Tuang8ee/SmartRecycleBin/Project/CAD/ThungRac/ThungKL_Nhua/AnhCocauNghienVoNhua_1.jpg

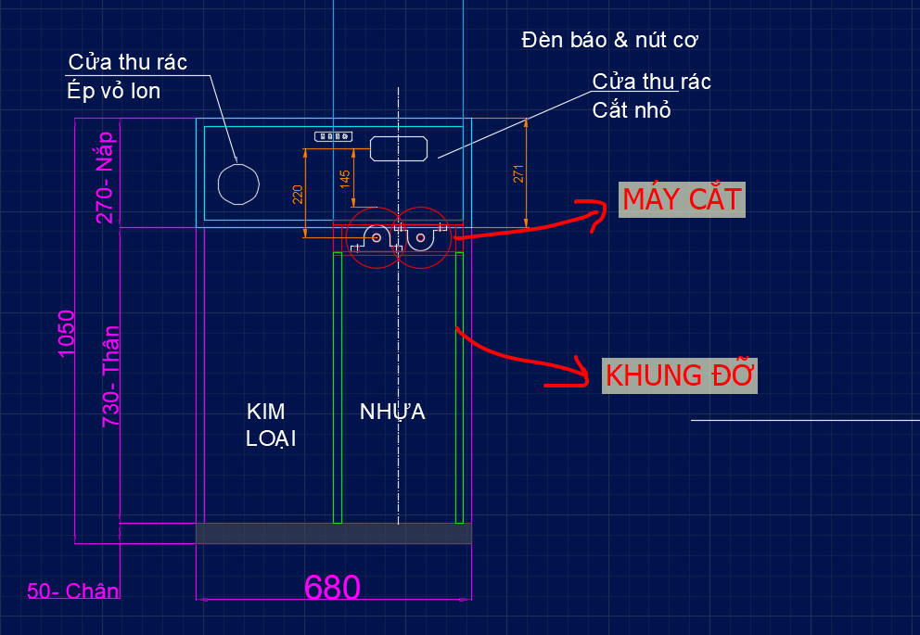
Project/CAD/ThungRac/ThungKL_Nhua/AnhCocauNghienVoNhua_1.jpg
