Tuang8ee/SmartRecycleBin/Project/CAD/ThungRac/ThungKL_Nhua/AnhCocauNghienVoNhua_2.jpg

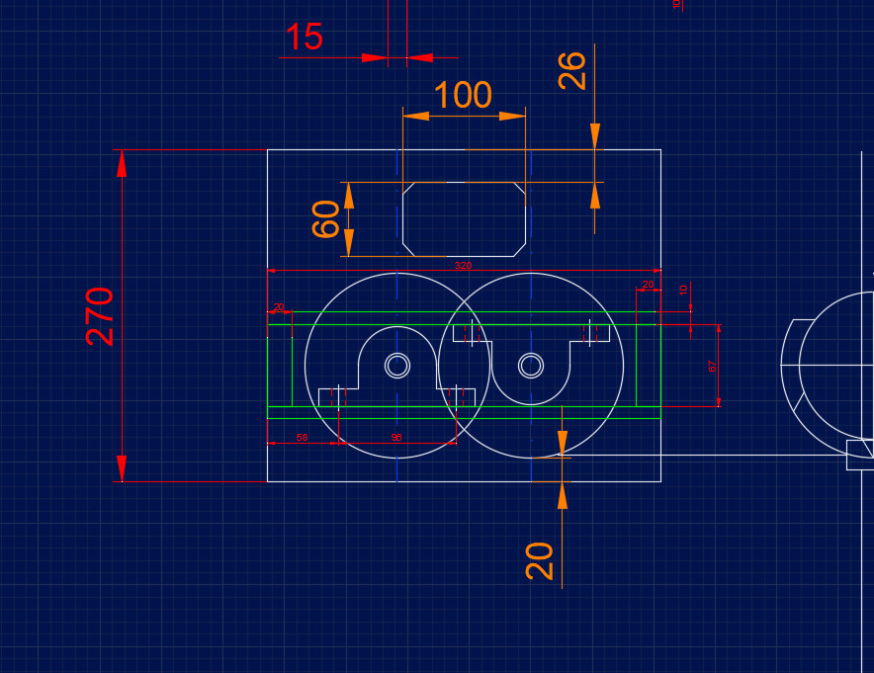
Project/CAD/ThungRac/ThungKL_Nhua/AnhCocauNghienVoNhua_2.jpg
