Tuang8ee/SmartRecycleBin/Report/IMG/z3350971797533_e74e3346405ee866cc10981217ea934d.jpg

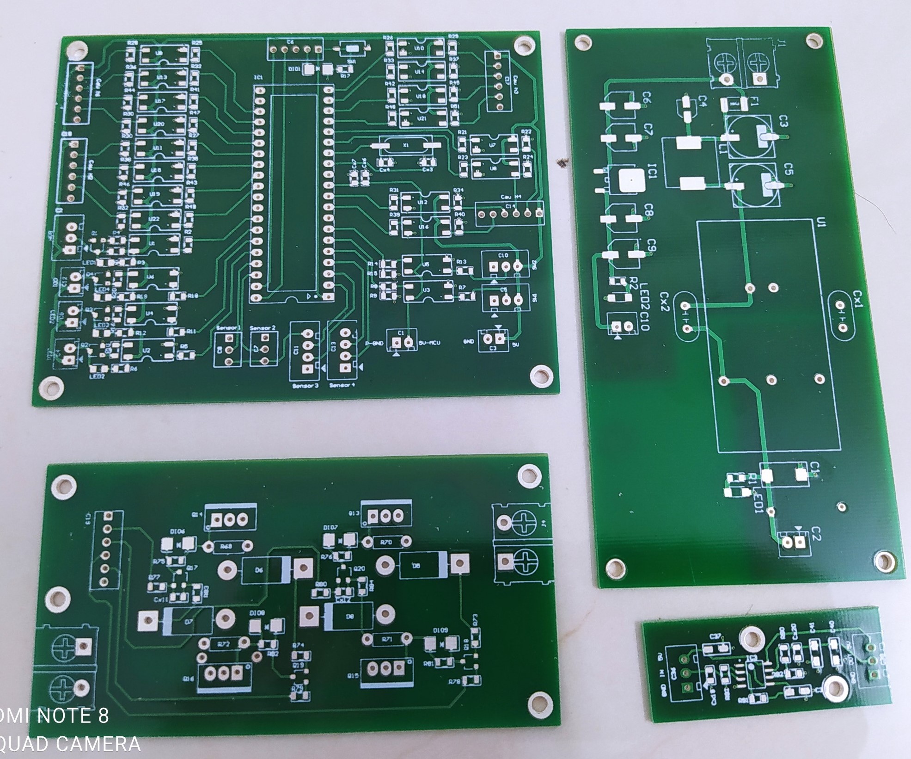
Report/IMG/z3350971797533_e74e3346405ee866cc10981217ea934d.jpg
