Tuang8ee/SmartRecycleBin/Report/IMG/z3350971799951_f81bc6857dea39808778af6e33a4ab04.jpg

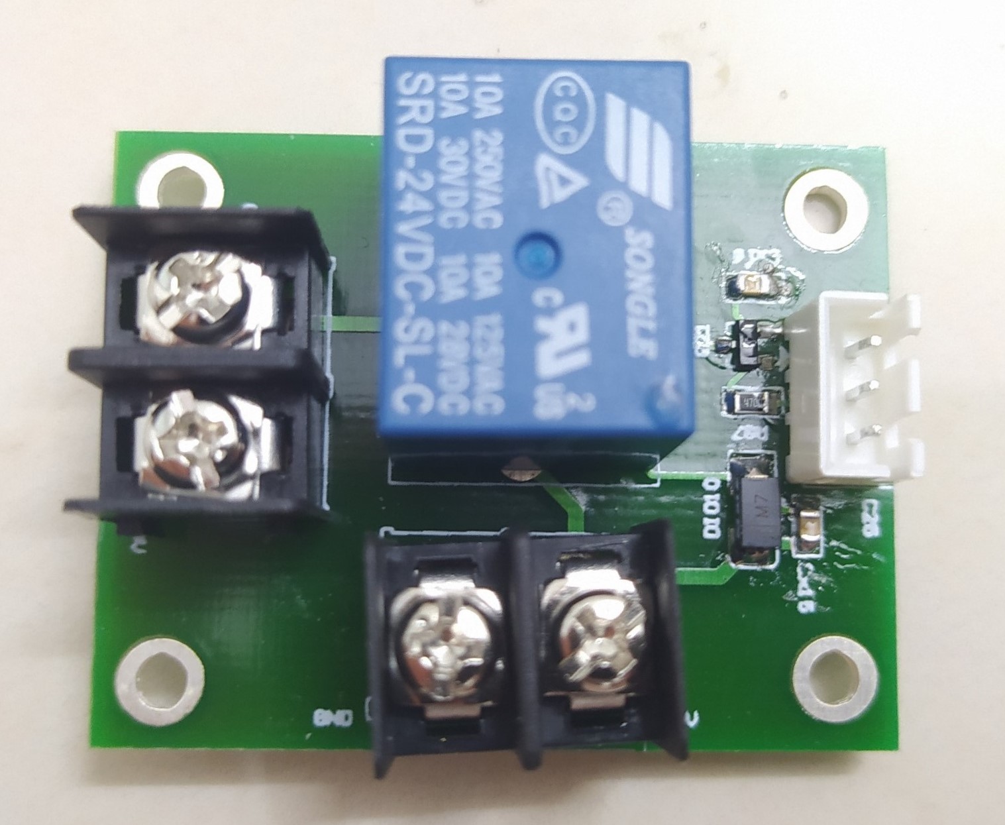
Report/IMG/z3350971799951_f81bc6857dea39808778af6e33a4ab04.jpg
