Tuang8ee/SmartRecycleBin/Report/IMG/z3350971800552_80eb1a36aaf828dc6509fbc643d5b15d.jpg

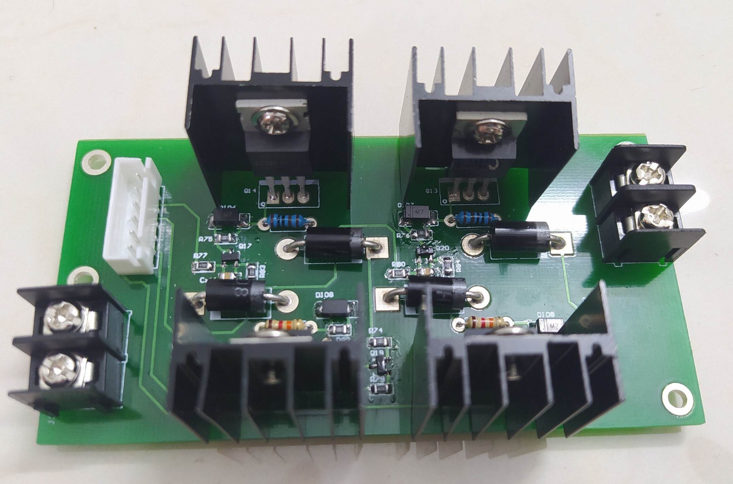
Report/IMG/z3350971800552_80eb1a36aaf828dc6509fbc643d5b15d.jpg
