Tuang8ee/SmartRecycleBin/Report/IMG/z3350971802485_70b66bd4bab3340eb6d8cfec86ee5f43.jpg

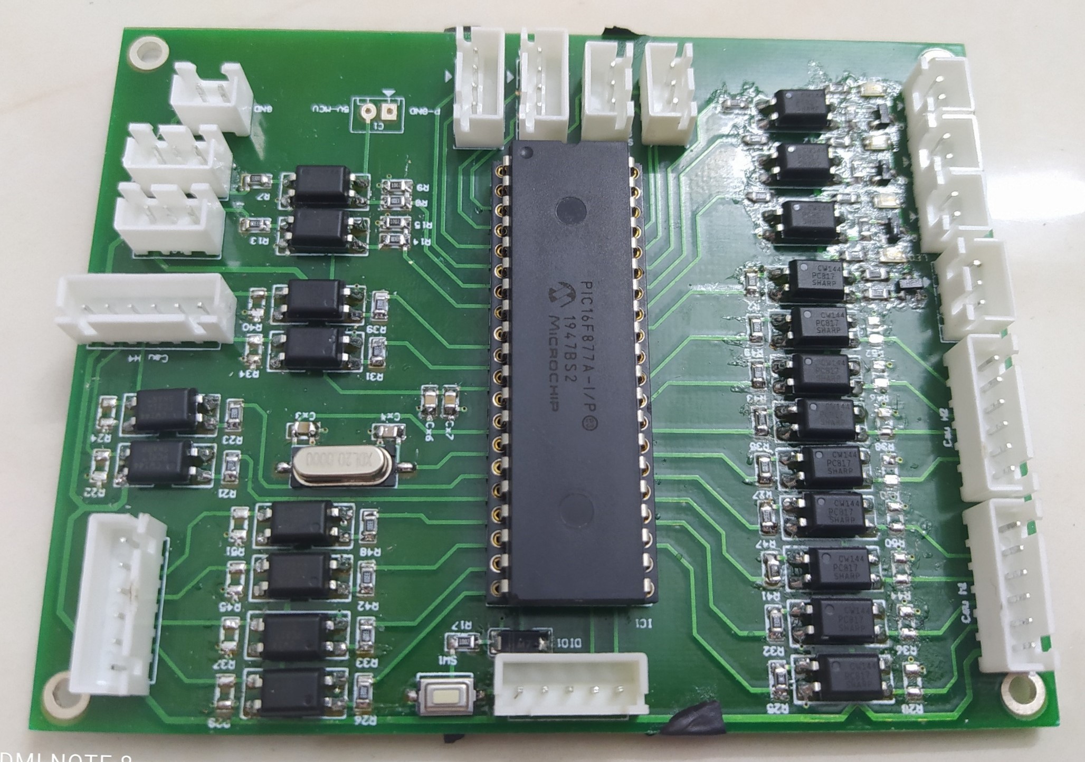
Report/IMG/z3350971802485_70b66bd4bab3340eb6d8cfec86ee5f43.jpg
