Tuang8ee/SmartRecycleBin/Report/IMG/z3350971803121_91358038da6f96965107a016737c2b8c.jpg

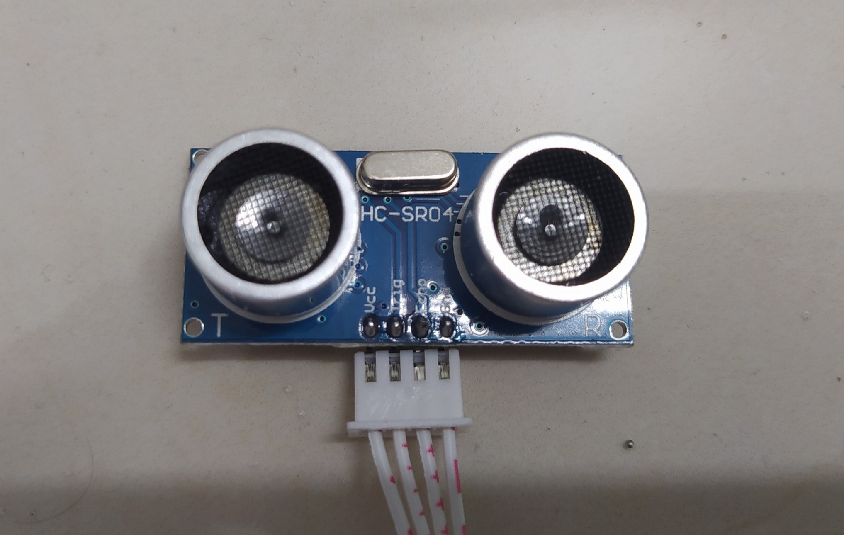
Report/IMG/z3350971803121_91358038da6f96965107a016737c2b8c.jpg
