Tuang8ee/SmartRecycleBin/Report/IMG/z3350971803122_7163d0be3d43af4151d32110a8dd91e1.jpg

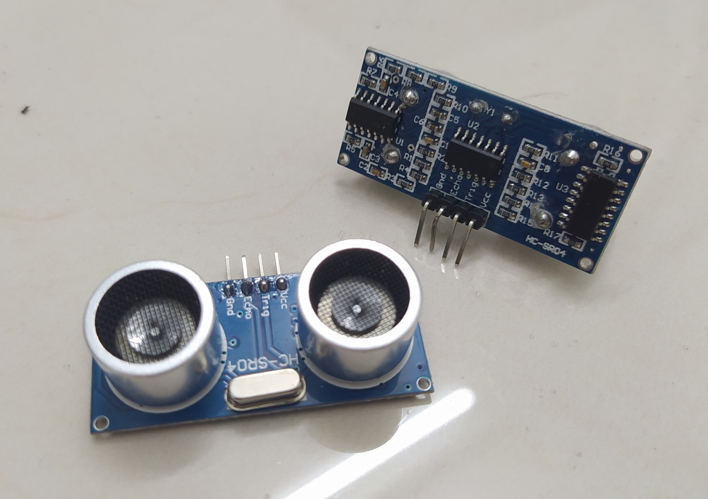
Report/IMG/z3350971803122_7163d0be3d43af4151d32110a8dd91e1.jpg
