Tuang8ee/SmartRecycleBin/Report/IMG/z3350971805743_a142735bbfeaa44c15cc64908d8d2765.jpg

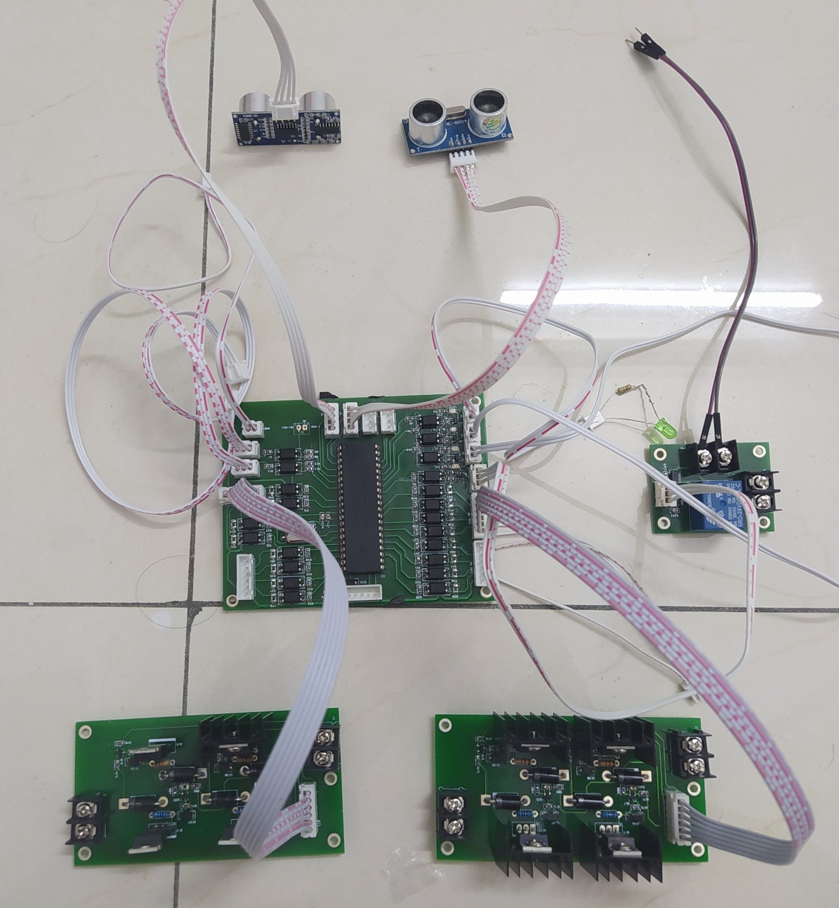
Report/IMG/z3350971805743_a142735bbfeaa44c15cc64908d8d2765.jpg
