Tuang8ee/SmartRecycleBin/Report/IMG/z3350971805745_b5374c409a4009194ae9360d5b574b62.jpg

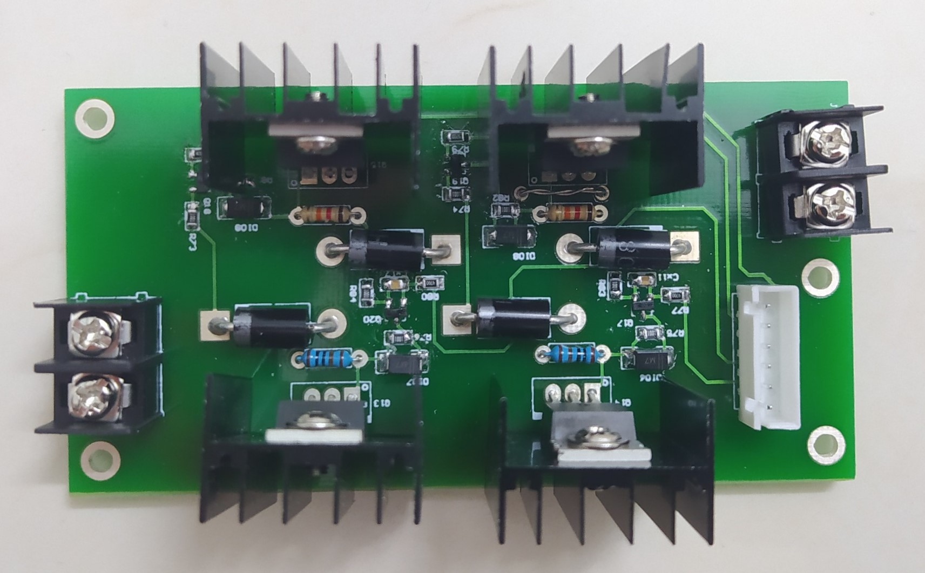
Report/IMG/z3350971805745_b5374c409a4009194ae9360d5b574b62.jpg
