Tuang8ee/SmartRecycleBin/Project/Code/SmartRecyleBin/SmartRecycleBin.Backup/Peripheral_Libs/Hearder/LoopProcess.h

/* 
 * File:   LoopProcess.h
 * Author: tuang
 *
 * Created on April 16, 2022, 8:50 AM
 */

#ifndef LOOPPROCESS_H
#define	LOOPPROCESS_H

#ifndef DEFINE_H
    #include "D:\Projects\Projects\MyWork\ThungRacThongMinh\SmartRecycleBin\Project\Code\SmartRecyleBin\SmartRecycleBin.VS\Peripheral_Libs\Hearder\define.h"
#endif

void Loop(volatile uint16_t *timeSysTick);
/*
 ================================== START CODE ============================
 */


#endif	/* LOOPPROCESS_H */
