Tuang8ee/SmartRecycleBin/Project/Code/SmartRecyleBin/SmartRecycleBin.Backup/Peripheral_Libs/Source/UART.c

/* 
 * File:   UART.h
 * Author: tuang
 *
 * Created on April 18, 2022, 9:37 PM
 */

#include "../Hearder/UART.h"
#ifndef _STRING_H
    #include "string.h"
#endif

void UART_BASE_Init(long baud)
{
    TRISC = 0X80;
    TXSTA = 0X24;
    RCSTA = 0X90;
    SPBRG = (_XTAL_FREQ / (long)(16UL * baud)) - 1;
}

void UART_WriteChar(char data)
{
    TXREG = data;
    while(TXIF == 0);
    TXIF = 0;
    while(TRMT != 1);
}
void UART_Writes(const char *data, size_t len)
{
    uint8_t i = 0;
    for(i = 0; i <= len; i++)
    {
        UART_WriteChar(data[i]);
    }
}

void UART_WriteStr(const char *data)
{
    uint8_t i = 0;
    size_t len = strlen(data);
    for(i = 0; i <= len; i++)
    {
        UART_WriteChar(data[i]);
    }
}
